iu2vwk-ita/morsebox-mini/morse.py

# Morse code table and its reverse - shared by server.py and exercise.py.
MORSE = {"A": ".-", "B": "-...", "C": "-.-.", "D": "-..", "E": ".",
         "F": "..-.", "G": "--.", "H": "....", "I": "..", "J": ".---",
         "K": "-.-", "L": ".-..", "M": "--", "N": "-.", "O": "---",
         "P": ".--.", "Q": "--.-", "R": ".-.", "S": "...", "T": "-",
         "U": "..-", "V": "...-", "W": ".--", "X": "-..-", "Y": "-.--",
         "Z": "--..", "0": "-----", "1": ".----", "2": "..---",
         "3": "...--", "4": "....-", "5": ".....", "6": "-....",
         "7": "--...", "8": "---..", "9": "----.", ".": ".-.-.-",
         ",": "--..--", "?": "..--..", "/": "-..-.", "=": "-...-",
         "+": ".-.-.", "-": "-....-", ":": "---...", "'": ".----.",
         '"': ".-..-.", "_": "..--.-", "$": "...-..-", "&": ".-...",
         "@": ".--.-.", "!": "-.-.--"}
FROM_MORSE = {v: k for k, v in MORSE.items()}
